ctu-mrs/mrs_hw_uvdar/UVDAR_Module/Documentation/figures/Connectors_bot.pdf

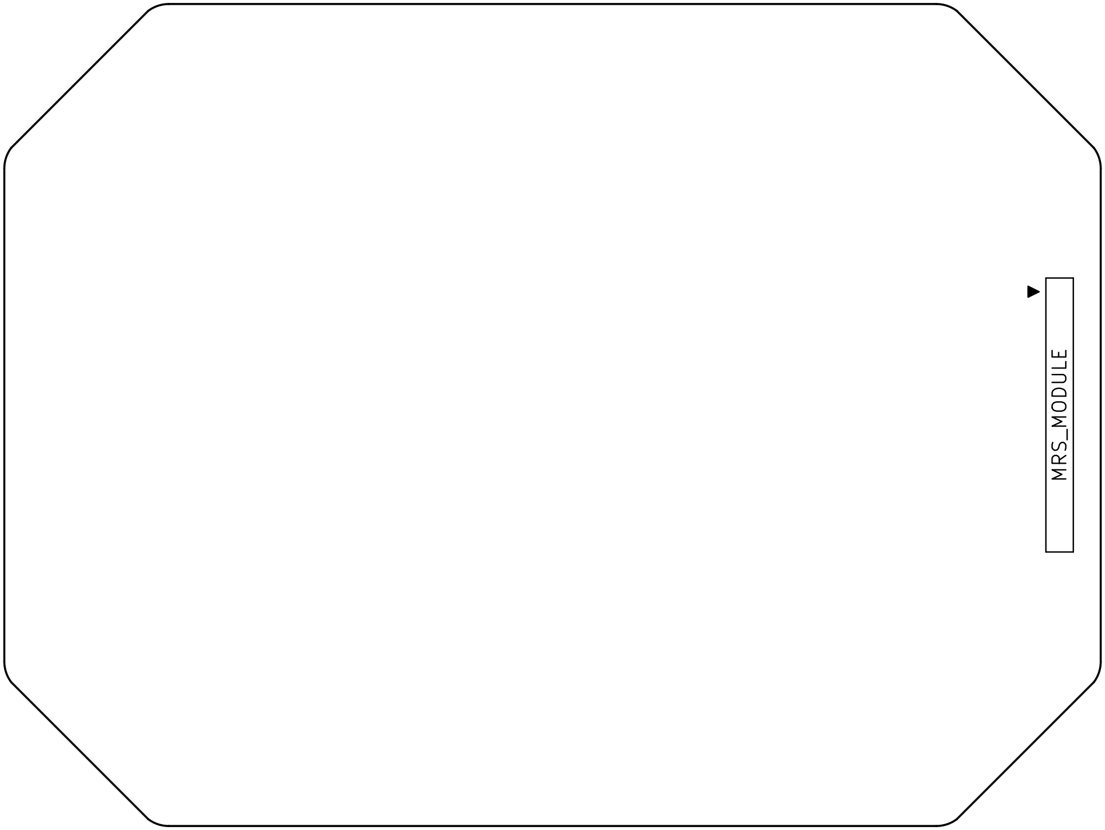
[picture p14: figure]
