ctu-mrs/mrs_hw_uvdar/UVDAR_Standalone/Documentation/figures/Dimensions.pdf

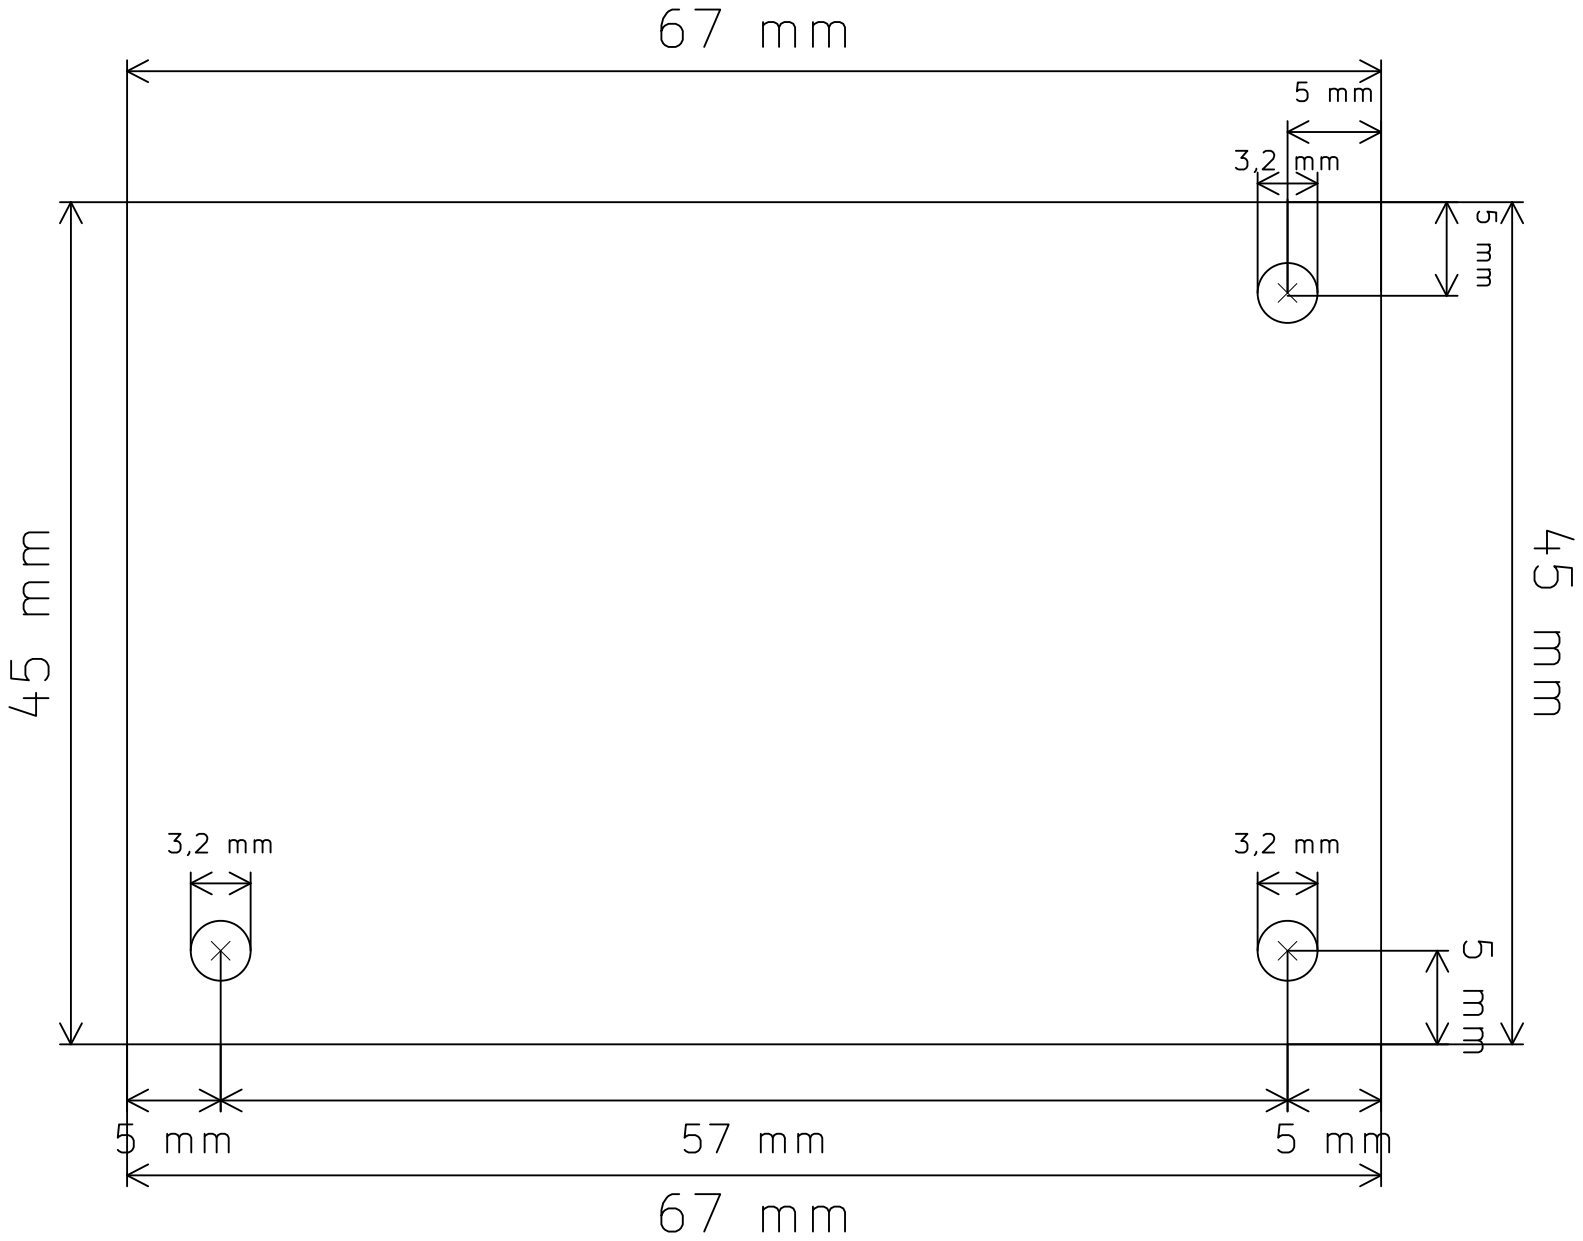
[picture p33: page 1]
