ctu-mrs/mrs_hw_uvdar/UVDAR_Module/Documentation/figures/Connectors_top.pdf

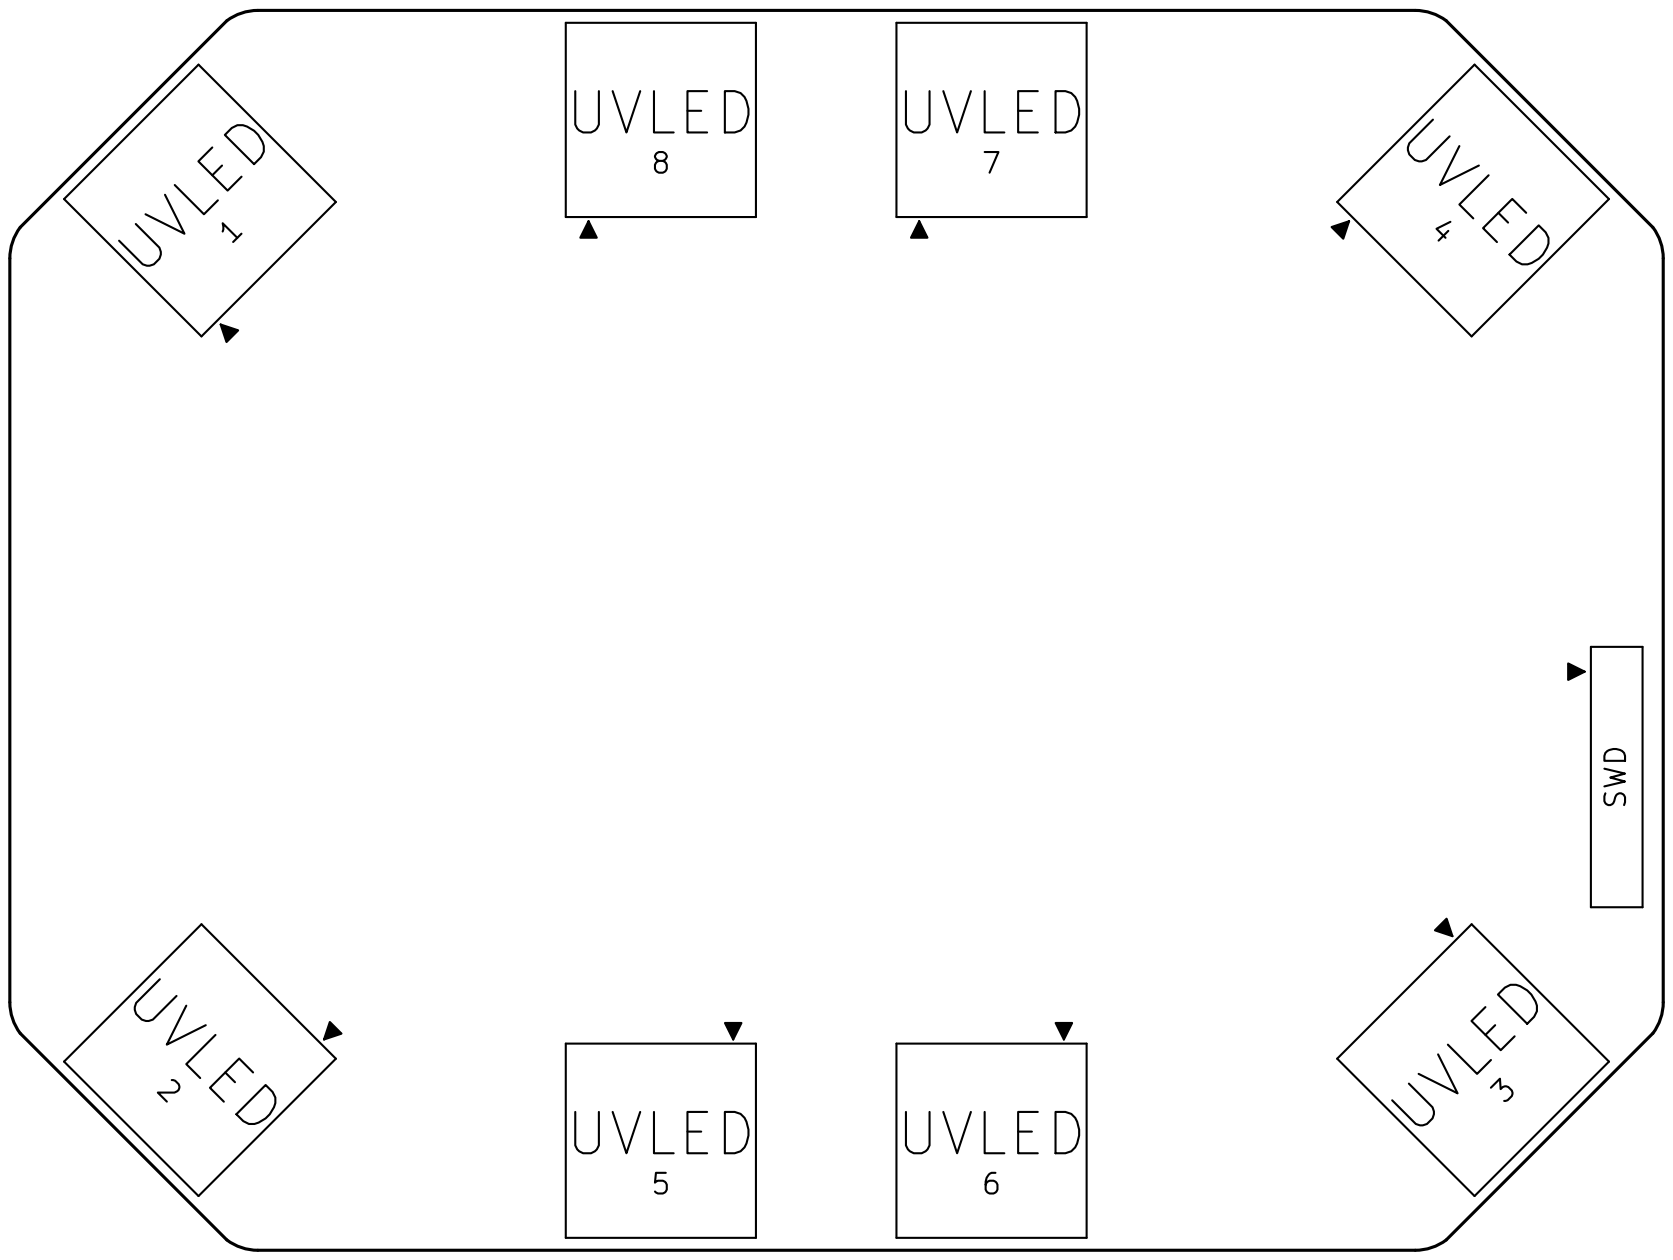
[picture p34: page 1]
