ctu-mrs/mrs_hw_uvdar/UVDAR_Module/Documentation/figures/Dimensions.pdf

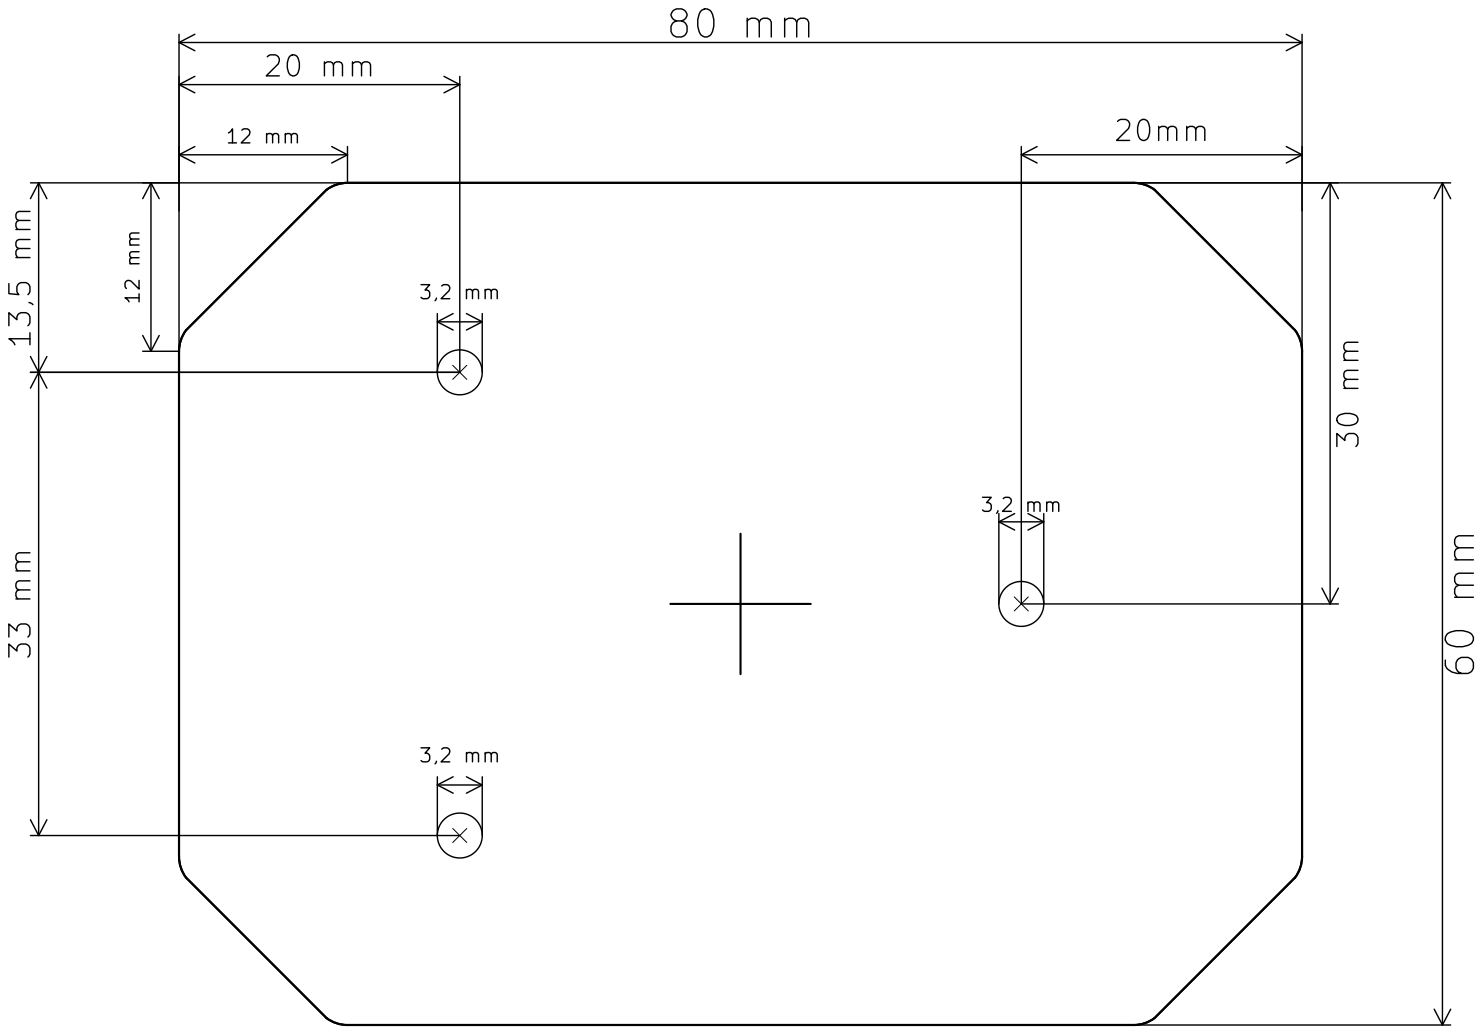
[picture p35: page 1]
